badjeff/moudabella/STLs/a4 - mcu clip.stl

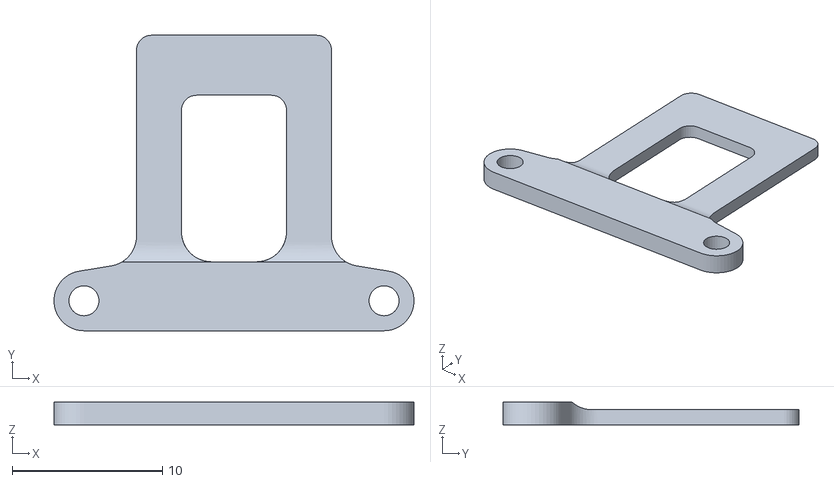
[picture p22: CAD file, 2024-11-09]
STLs/a4 - mcu clip.stl
24.0 x 19.7 x 1.50
