badjeff/moudabella/STLs/b4 - side arms clip R.stl

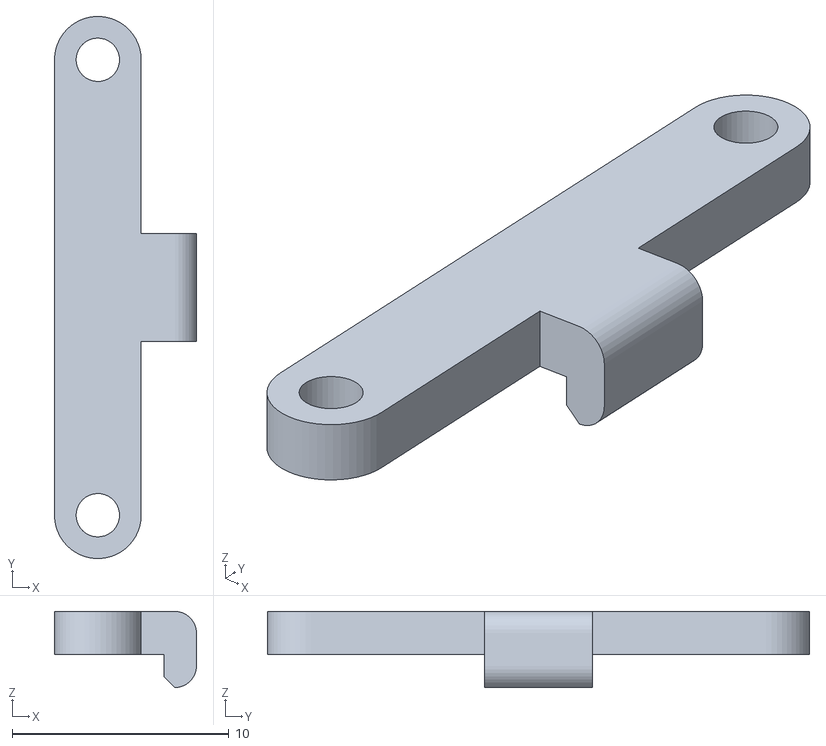
[picture p23: CAD file, 2024-11-09]
STLs/b4 - side arms clip R.stl
6.55 x 25.0 x 3.51
