badjeff/moudabella/STLs/d2 - side buttons left.stl

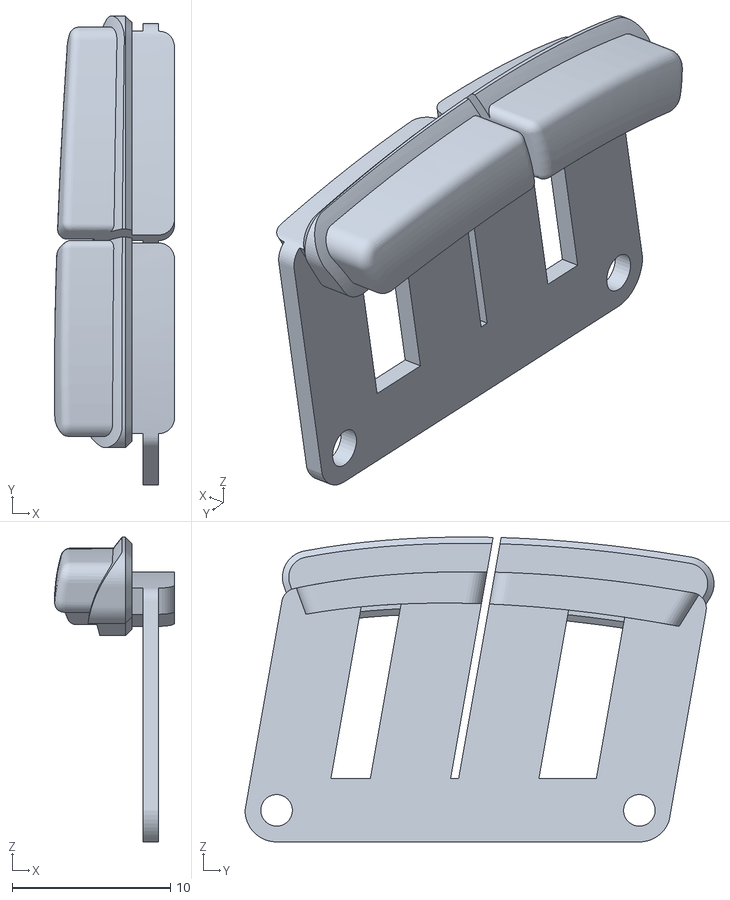
[picture p24: CAD file, 2024-11-09]
STLs/d2 - side buttons left.stl
7.59 x 29.7 x 19.3
