badjeff/moudabella/STLs/c6 - battery cover.stl

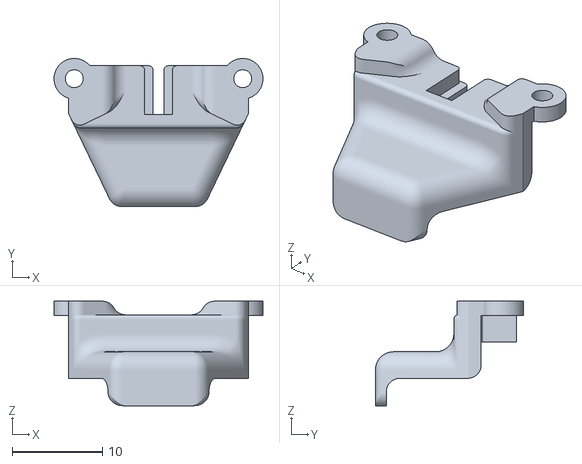
[picture p25: CAD file, 2024-11-09]
STLs/c6 - battery cover.stl
23.2 x 16.4 x 11.6
