badjeff/moudabella/STLs/a3 - R btn mount.stl

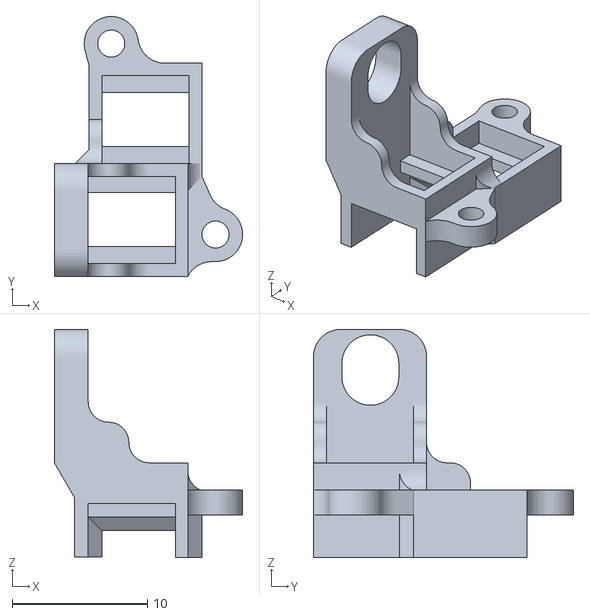
[picture p26: CAD file, 2024-11-09]
STLs/a3 - R btn mount.stl
13.9 x 19.2 x 16.9
