badjeff/moudabella/STLs/a7 - shell front.stl

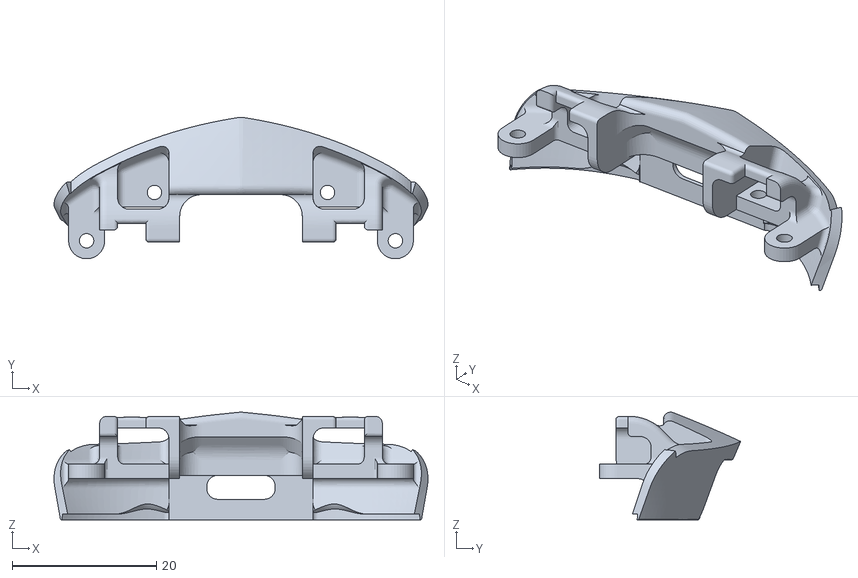
[picture p27: CAD file, 2024-11-09]
STLs/a7 - shell front.stl
51.9 x 19.6 x 14.9
